NemoAndrea/lasercut-lamp/cuttable-files/rib_7.dxf

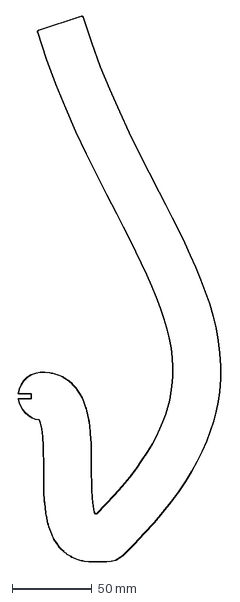
[picture p18: CAD file, 2024-08-06]
cuttable-files/rib_7.dxf
127.1 x 341.3 mm
