NemoAndrea/lasercut-lamp/cuttable-files/rib_3.dxf

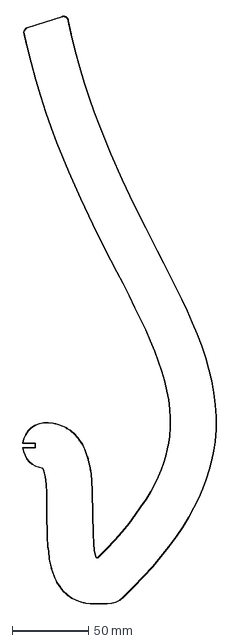
[picture p19: CAD file, 2024-08-06]
cuttable-files/rib_3.dxf
127.1 x 385.0 mm
