NemoAndrea/lasercut-lamp/cuttable-files/rib_12.dxf

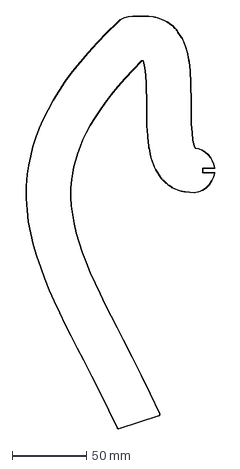
[picture p20: CAD file, 2024-08-06]
cuttable-files/rib_12.dxf
127.1 x 277.5 mm
