NemoAndrea/lasercut-lamp/cuttable-files/lamp-ring.dxf

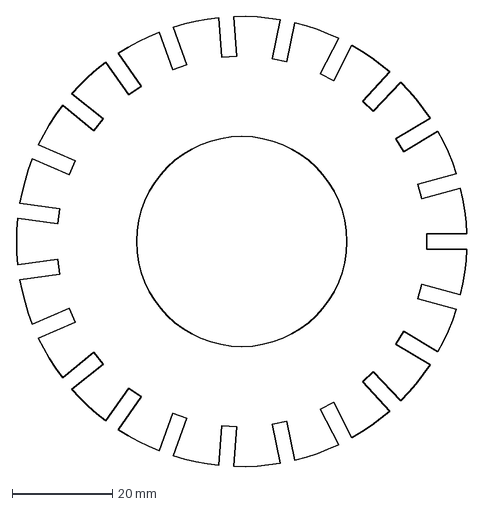
[picture p21: CAD file, 2024-08-06]
cuttable-files/lamp-ring.dxf
90.1 x 90.2 mm
