NemoAndrea/lasercut-lamp/cuttable-files/rib_8.dxf

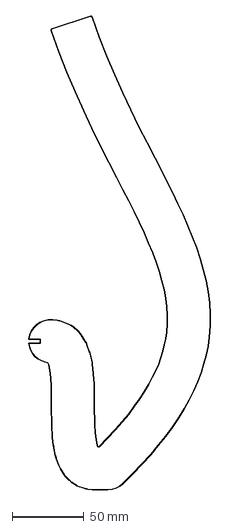
[picture p22: CAD file, 2024-08-06]
cuttable-files/rib_8.dxf
127.1 x 330.5 mm
