NemoAndrea/lasercut-lamp/cuttable-files/rib_4.dxf

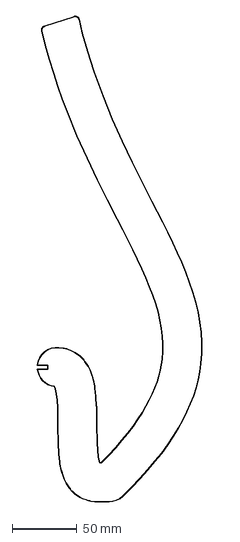
[picture p23: CAD file, 2024-08-06]
cuttable-files/rib_4.dxf
127.1 x 373.8 mm
