NemoAndrea/lasercut-lamp/cuttable-files/rib_6.dxf

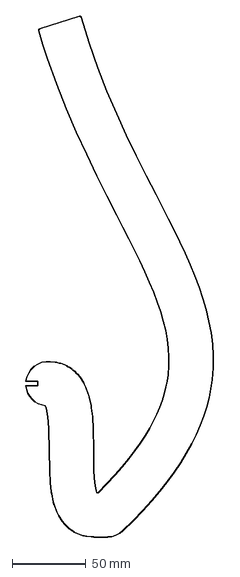
[picture p24: CAD file, 2024-08-06]
cuttable-files/rib_6.dxf
127.1 x 352.2 mm
