NemoAndrea/lasercut-lamp/cuttable-files/rib_2.dxf

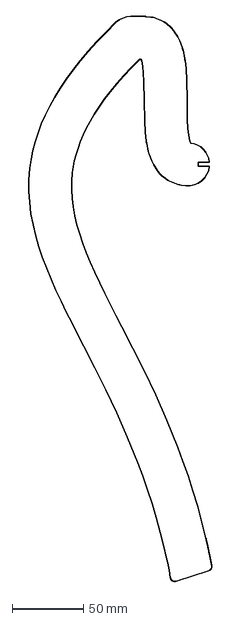
[picture p25: CAD file, 2024-08-06]
cuttable-files/rib_2.dxf
128.9 x 396.2 mm
