NemoAndrea/lasercut-lamp/cuttable-files/rib_9.dxf

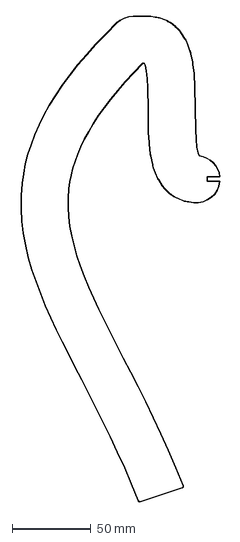
[picture p26: CAD file, 2024-08-06]
cuttable-files/rib_9.dxf
127.1 x 309.0 mm
