NemoAndrea/lasercut-lamp/cuttable-files/rib_22.dxf

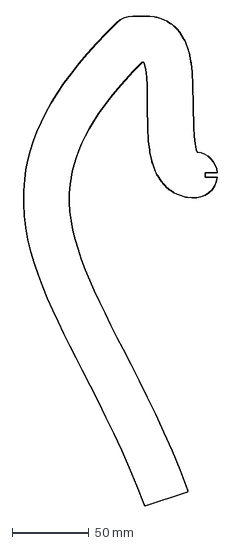
[picture p27: CAD file, 2024-08-06]
cuttable-files/rib_22.dxf
127.1 x 319.7 mm
